HandHeldLegend/GC-Ultimate/CAD/Printable/Split Dpad.stl

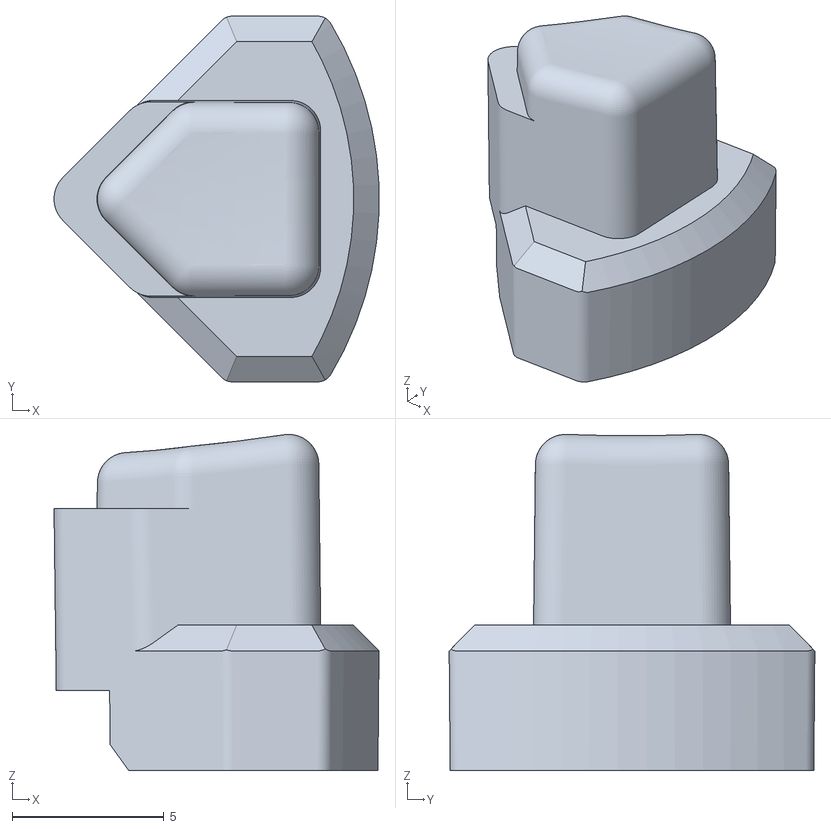
[picture p18: CAD file, 2025-07-15]
CAD/Printable/Split Dpad.stl
10.7 x 12.1 x 11.1
