HandHeldLegend/GC-Ultimate/CAD/Printable/Membrane Trigger Holder.stl

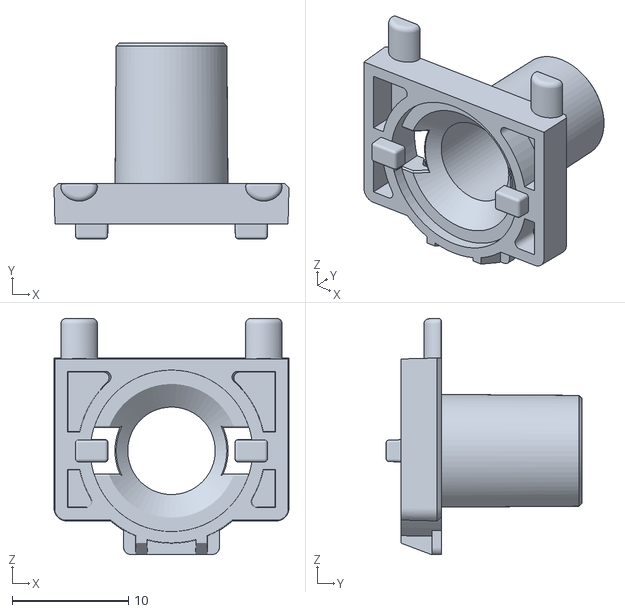
[picture p19: CAD file, 2025-07-15]
CAD/Printable/Membrane Trigger Holder.stl
20.2 x 16.9 x 20.3
