HandHeldLegend/GC-Ultimate/CAD/Printable/Mechanical Trigger Bracket.stl

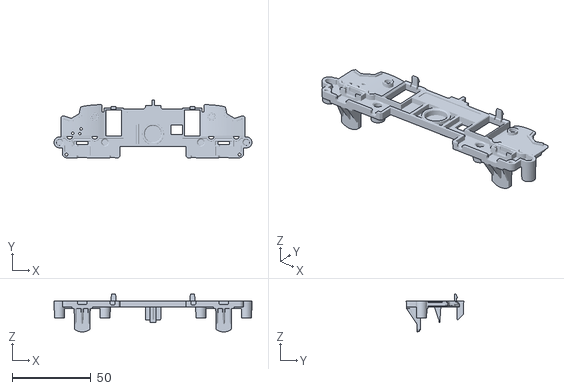
[picture p20: CAD file, 2025-07-15]
CAD/Printable/Mechanical Trigger Bracket.stl
125.9 x 36.6 x 24.2
