HandHeldLegend/GC-Ultimate/CAD/Printable/Light Pipe.stl

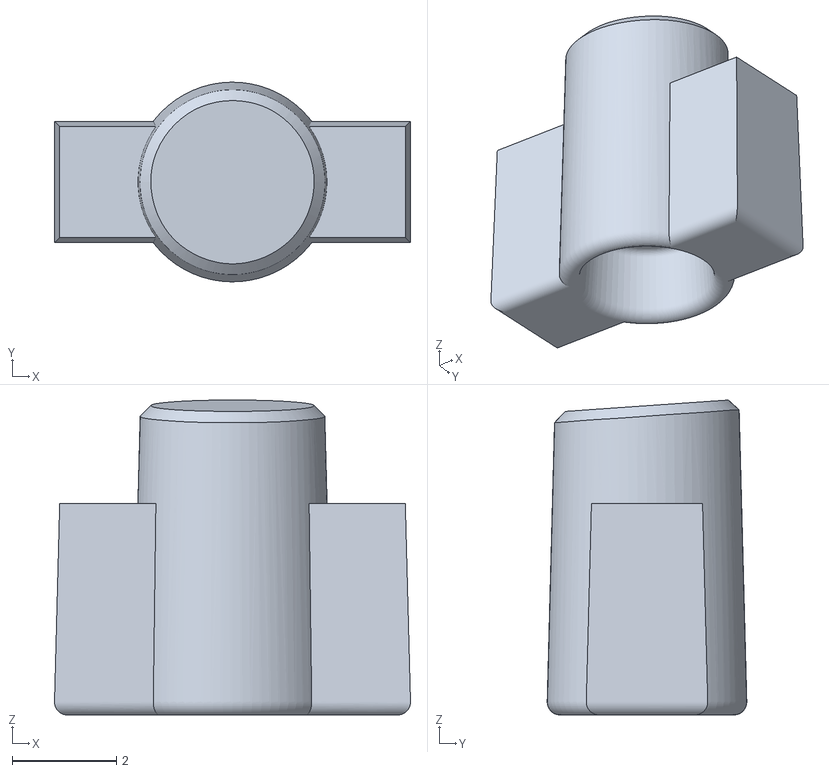
[picture p21: CAD file, 2025-07-15]
CAD/Printable/Light Pipe.stl
6.83 x 3.83 x 6.04
